bubnikv/BlinkySWR/design/ltspice/blinky-diode-curve-shorted.asc

C1: cap; 1n
C2: cap; 1n
C_SH: cap; 14p
D1: schottky; DI_1N5711
R1: res; 25
R2: res; 25
R3: res; 50
R4: res; 50
R5: res; 50
R6: res; 150k
R7: res; 10k
R_ADC: res; 50k
V1: voltage; SINE(0 20 7MEG)
Named nets: 0, ADC, load_hi, src_hi, src_lo
.tran 0.00000001 .001 0.000999
.include spicemodels_schottky_diodes.txt
At 1W input power and SWR 1:1, the ADC voltage will be 225mV,
peak diode current will be 0.46mA
