bubnikv/BlinkySWR/design/ltspice/blinky-power-supply-10W-open.asc

C1: cap; 1n
D1: schottky; DI_1N5711
D2: schottky; DI_1N5711
R1: res; 25
R2: res; 25
R3: res; 50
R4: res; 50
R5: res; 1Meg
R6: res; 14500
V1: voltage; SINE(0 63.24 7MEG)
V2: voltage; 2.4
Named nets: 0, src_hi, src_lo, load_hi
.tran 0 .001 0.0009
.include spicemodels_schottky_diodes.txt
At 10W input power and SWR 1:infinity (open), and at 2.4V / 1.2mA recovered DC power,
the diode peak current is 13mA, which is 3% of 427mA input peak current.
3rd harmonic introduced by the power recovery circuit is -35dB below the carrier.
