bubnikv/BlinkySWR/design/ltspice/blinky-diode-curve-open.asc

C1: cap; 1n
C2: cap; 1n
C_SH: cap; 10p
D1: schottky; DI_1N5711
R1: res; 25
R2: res; 25
R3: res; 50
R4: res; 50
R5: res; 1Meg
R6: res; 39k
R7: res; 2.2k
R_ADC: res; 10k
V1: voltage; SINE(0 20 7MEG)
Named nets: 0, ADC, load_hi, src_hi, src_lo
.tran 0.00000001 .001 0.000999
.include spicemodels_schottky_diodes.txt
